frsaba/mcguitarpedal/preamp/SPICE Files/LTspice/Preamp_noise_noninv_filter_first.asc

C1: cap; 470n
C2: cap; 570p
C3: cap; 470n
C4: cap; 470n
C5: cap; 10µ
Coil: ind; 2.35
R2: res; {R}
R3: res; 200k
R4: res; {R}
R5: res; {R}
R6: res; {R}
R8: res; 100k
R9: res; 100k
R: res; 8.2k
Rf: res; 2k
Rg: res; 500
STAGE1: StageA_LowPassSallenKey_ADA4898
U1: UniversalOpAmp
V1: voltage; 5
V2: voltage; 9
V3: voltage; 0
V4: voltage; 3.3
VIN: voltage; SINE(0 100m 3k); AC 1
Named nets: 0, Vp, Vn, Vref, 3.3V, PREAMP_OUT, STAGE1_OUT, PREAMP_IN
.ac dec 100 1 150k
.save V(*?*) I(*?*)
If you're having trouble with simulation try the following:
 
- Ensure that LTspice circuit folder is unzipped.  LTspice won't 
be able to locate subcircuits if the folders are still zipped.
 
- Update LTspice - devices that have been recently added to LTspice
won't be available unless you update by clicking Tools -> Sync Release.
.noise V(PREAMP_OUT) VIN dec 100 2k 1Meg
.param R=100k
.tran 0 15ms 0 100ns
.lib LME49710.lib
