frsaba/mcguitarpedal/preamp/SPICE Files/LTspice/lme49710.asc

Rf6: res; 100
U1: LME49710
V1: voltage; 17
V2: voltage; -17
Vin_source: voltage; SINE(0 1 1k); AC 1
Named nets: 0, v+, v-, Vin
.tran 10m
;.ac oct 100 20 20k
