frsaba/mcguitarpedal/preamp/SPICE Files/LTspice/Preamp_noise._switched.asc

C1: cap; 470n
C2: cap; 570p
C3: cap; 470n
C4: cap; 470n
Coil: ind; 2.35
Pot: res; 2.5k
R1: res; {R}
R2: res; {R}
R3: res; 200k
R4: res; {R}
R6: res; 2.5k
R8: res; 100k
R9: res; 100k
R: res; 8.2k
STAGE1: StageA_LowPassSallenKey_ADA4898
U1: ADA4898
V1: voltage; 5
V2: voltage; 9
V3: voltage; 0
V4: voltage; 3.3
VIN: voltage; SINE(5 100m 1.95k); AC 1
Named nets: 0, Vp, Vn, Vref, 3.3V, FILTER_IN, PREAMP_OUT
.ac dec 100 10 250k
.save V(*?*) I(*?*)
If you're having trouble with simulation try the following:
 
- Ensure that LTspice circuit folder is unzipped.  LTspice won't 
be able to locate subcircuits if the folders are still zipped.
 
- Update LTspice - devices that have been recently added to LTspice
won't be available unless you update by clicking Tools -> Sync Release.
.noise V(PREAMP_OUT) VIN dec 100 2k 1Meg
.param R=1Meg
