frsaba/mcguitarpedal/preamp/SPICE Files/LTspice/StageA_LowPassSallenKey_ADA4898.asc

C1: cap; 4.7n
C2: cap; 2.2n
R1: res; 1k
R2: res; 2.2k
U1: ADA4898
Named nets: V+, V-, OUT, IN, REF, Vp
This subcircuit is not simulatable.  
Please open one of the 
"Filter Design*.asc" schematics to 
simulate your Filter Wizard design.
