frsaba/mcguitarpedal/preamp/SPICE Files/LTspice/TransientAnalysis.asc

STAGE1: StageA_LowPassSallenKey_ADA4898
V1: voltage; 0
V2: voltage; 9
V3: voltage; 0
VIN: voltage; PULSE(4.5 5 0 1n 1n 1 2); AC 1
Named nets: 0, Vp, Vn, OUT, Vref, IN
.TRAN 200u 
.save V(*?*) I(*?*)
If you're having trouble with simulation try the following:
 
- Ensure that LTspice circuit folder is unzipped.  LTspice won't 
be able to locate subcircuits if the folders are still zipped.
 
- Update LTspice - devices that have been recently added to LTspice
won't be available unless you update by clicking Tools -> Sync Release.
